gavinlyonsrepo/LR_meter_arduino/documentation/eagle/LR_meter.sch

## EAGLE design documentation/eagle/LR_meter.sch (2019-05-04)

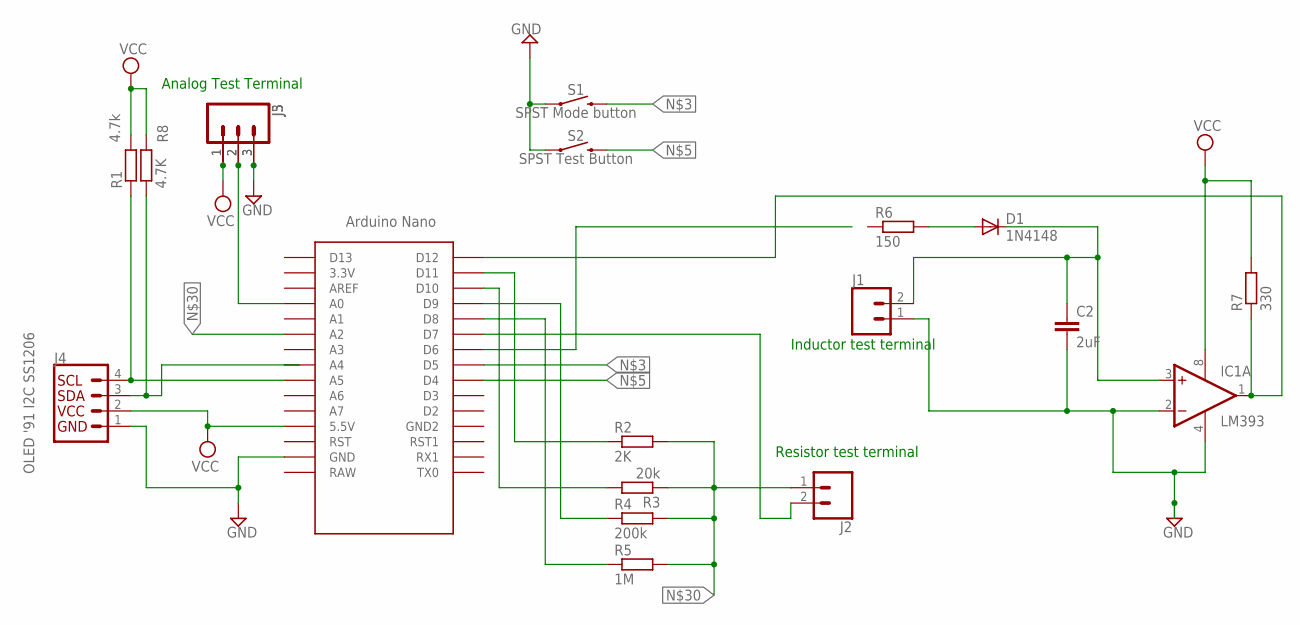
[picture p4: schematic LR_meter.sch]

Parts:
C2: 2uF; C5B2.5
D1: 1N4148; DO35-10
IC1: LM393; DIL08
J1, J2: CONN_02; 1X02
J3, J5: CONN_031X03_SMD_RA_MALE_POST_SMALLEST; 1X03_SMD_RA_MALE_POST_SMALLEST
J4: OLED '91 I2C SS1206; 1X04
R1: 4.7k; 0207/10
R2: 2K; 0207/10
R3: 20k; 0207/10
R4: 200k; 0207/10
R5: 1M; 0207/10
R6: 150; 0207/10
R7: 330; 0207/15
R8: 4.7K; 0207/10
S1: SPST Mode button; TACTILE_SWITCH_PTH_6.0MM_KIT
S2: SPST Test Button; TACTILE_SWITCH_PTH_6.0MM_KIT
U$1: NANO

Connections:
GND: C2.2, IC1.2 (-IN), IC1.4 (V-), J1.1, J3.3, J4.1, J5.3, S1.1, S2.1, U$1.GND
unnamed: J4.4, R1.1, U$1.A5
unnamed: J4.3, R8.1, U$1.A4
unnamed: R2.1, U$1.D11
unnamed: R3.2, U$1.D10
unnamed: R4.1, U$1.D9
unnamed: R5.1, U$1.D8
unnamed: J2.2, U$1.D7
unnamed: C2.1, D1.C, IC1.3 (+IN), J1.2
unnamed: D1.A, R6.2
unnamed: IC1.1 (OUT), R7.1, U$1.D12
unnamed: J2.1, R2.2, R3.1, R4.2, R5.2
VCC: IC1.8 (V+), J3.1, J4.2, J5.1, R1.2, R7.2, R8.2, U$1.5V (5.5V)
VRX: J3.2, J5.2, U$1.A0

Notes on the sheet:
Analog Test Terminal
Inductor test terminal
Resistor test terminal
